AnalogDragon/Taiko-Input/QT-APP/APP1_Taiko_IO_Setting/images/tk.png

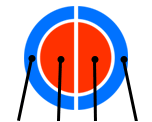
QT-APP/APP1_Taiko_IO_Setting/images/tk.png
